sequ3ster/esp_flying_delorean/EspFlyingDelorean/animation.h

static const uint8_t PROGMEM

  eq1_bmp[] =
  { B0000000,
    B0000000,
    B0000000,
    B0000000,
    B0000000,
    B0000000,
    B0000000,
    B0000000,
    B0000000,
    B0000001,
    B0010001,
    B1011011,
    B1011111,
    B1111111,
    B1111111 },
  eq2_bmp[] =
  { B0000000,
    B0000000,
    B0000000,
    B0000000,
    B0000000,
    B0000000,
    B0000000,
    B0000000,
    B0000000,
    B0000000,
    B1000001,
    B1010101,
    B1111111,
    B1111111,
    B1111111 },
  eq3_bmp[] =
  { B0000000,
    B0000000,
    B0000000,
    B0000000,
    B0000000,
    B0000000,
    B0000000,
    B0000000,
    B0000000,
    B1000001,
    B1000101,
    B1110101,
    B1110111,
    B1111111,
    B1111111 },
  eq4_bmp[] =
  { B0000000,
    B0000000,
    B0000000,
    B0000000,
    B0000000,
    B0000000,
    B0000000,
    B0000000,
    B1000001,
    B1010001,
    B1010001,
    B1110111,
    B1110111,
    B1111111,
    B1111111 },
  eq5_bmp[] =
  { B0000000,
    B0000000,
    B0000000,
    B0000000,
    B0000000,
    B0000000,
    B0000000,
    B1000001,
    B1010001,
    B1010001,
    B1010101,
    B1110101,
    B1110111,
    B1110111,
    B1111111 },
  eq6_bmp[] =
  { B0000000,
    B0000000,
    B0000000,
    B0000000,
    B0000000,
    B0000000,
    B1010000,
    B1010000,
    B1010001,
    B1010101,
    B1010101,
    B1110111,
    B1110111,
    B1110111,
    B1110111 },  
  eq7_bmp[] =
  { B0000000,
    B1000000,
    B1000000,
    B1000000,
    B1010000,
    B1010000,
    B1010000,
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
    B0000000,
    B0000000,
    B0000000 },  
  eq19_inv_bmp[] =
  { B1111111,
    B1111111,
    B1110111,
    B1110111,
    B1010101,
    B0010101,
    B0010001,
    B0010001,
    B0000001,
    B0000000,
    B0000000,
    B0000000,
    B0000000,
    B0000000,
    B0000000 },
  eq20_inv_bmp[] =
  { B1111111,
    B1111111,
    B1111111,
    B1111111,
    B1111111,
    B0111111,
    B0110011,
    B0110010,
    B0100000,
    B0100000,
    B0100000,
    B0000000,
    B0000000,
    B0000000,
    B0000000 };
